jonahjlee/ccat850-led-mapping/collimator/CCAT_850GHz_si_array_mount_202501.SLDPRT

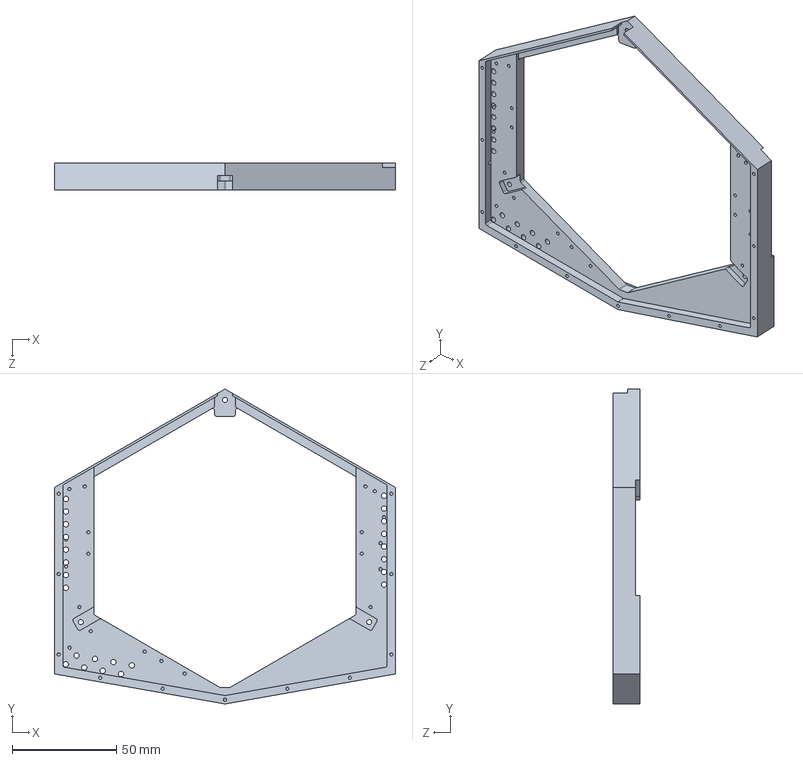
[picture p15: CAD file, 2025-03-10]
collimator/CCAT_850GHz_si_array_mount_202501.SLDPRT
163.9 x 151.4 x 12.8 mm
