jonahjlee/ccat850-led-mapping/collimator/thermal_flex_outer_202501.SLDPRT

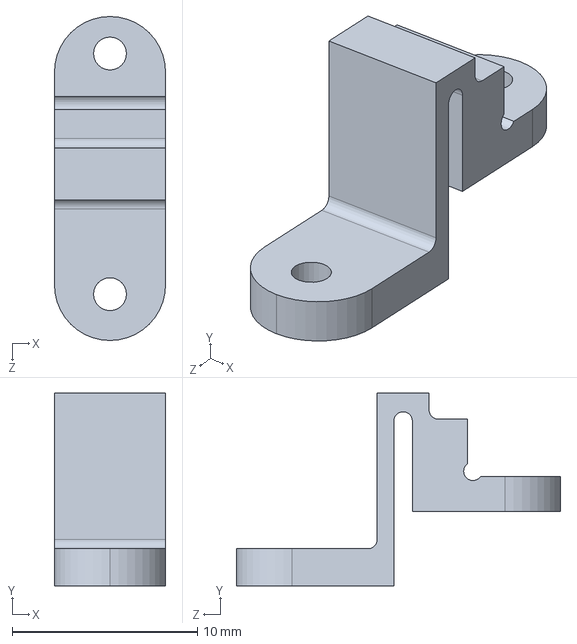
[picture p16: CAD file, 2025-03-10]
collimator/thermal_flex_outer_202501.SLDPRT
6.00 x 10.4 x 17.5 mm
